nexxyz/octessera/docs/menu-tree-spec.md

# Menu Tree Spec

This file is part of the authoritative menu/control spec rooted at `menu-and-controls-spec.md`. Keep it in sync with native menu tree changes.

This is the canonical index for the full menu tree. The split-out section files below are canonical parts of this spec and exist to keep each prose file navigable.

## Menu Tree (Full)

### Root Menu

```
Root (group)
├── Build (group)
├── Link (group)
├── Shape (group)
├── Play (group)
├── [spacer] (visual separator)
└── System (group)
```

## Split-out sections

- [Build](menu-tree/build.md)
- [Link](menu-tree/link.md)
- [Shape](menu-tree/shape.md)
- [Play](menu-tree/play.md)
- [System](menu-tree/system.md)

The Shape FX bus tree stores Duck `Source Tap` as `pre|post` and displays it as `Pre|Post`; omitted legacy values behave as `Pre`. Exact tap points and excluded stages are defined in [Shape routing semantics](menu-tree/shape.md#routing-semantics).

Short breadcrumb forms use `B`, `L`, `S`, and `P` for Build, Link, Shape, and Play.

The System section puts the dynamic Load Preset shortcut first, followed by Recording, Notes, MIDI,
Audio, UI, conditional SD Card 2, conditional HDMI Video, conditional Bluetooth, Saves, Setup, and Reset. The direct actions
Panic, Sys. Info, Basic Help, Reboot, and Shutdown follow the groups in that order. There is no
duplicate direct Save Current row; `System > Saves > Library > Save Current` is the only Save Current
row. Audio orders conditional USB Audio, conditional HDMI Audio, Master Vol, conditional Perf. Mode,
Polyphony, and Engine; Master Vol keeps key `masterVolume`.
SD Card 2, HDMI Video, and Bluetooth are board-only groups and are omitted on desktop. USB Role is a
Raspberry-capability-only child of Setup before Updates. The complete resolved System order and every
recursive branch are in the [System split-out tree](menu-tree/system.md).

The root Load Preset group contains a `(none)` refresh action and one confirmed action
for each named preset. The same named list remains available under
`System > Saves > Library > Load`.

`System > Notes` owns `Note Length`, `Vel Scale`, and `Vel Curve` with their
existing keys and semantics. `System > Audio` owns `Master Vol`, the supported USB and HDMI audio
mirrors, `Perf. Mode`, `Polyphony`, and `Engine`. `Perf. Mode` is visible on Raspberry and Orange
and displays compact `Lat | Cap` labels for the full `Latency | Capacity` choices; desktop hides it
and all Jack/USB/HDMI/SD2 device controls. `Polyphony` keeps the existing
`sound.voiceStealingMode` values `fixed12`, `fixed16`, `auto-soft`,
`auto-balanced`, `auto-hard`, and `none`. `Engine` contains CPU Warn % and Bus
Idle with their existing keys and values, plus Buf Frames where the
performance-mode capability is unavailable.

`System > MIDI` contains `MIDI Active`, then the conditional `MIDI Host` and `USB Device` groups,
then `Sync / Clock`. `MIDI Host` contains dynamic `MIDI Out` followed by `MIDI In`; it is visible
on desktop and Orange, and on Raspberry only in Host role. `USB Device` contains `USB MIDI`; it is
visible on Orange and on Raspberry only in Gadget role. `MIDI Active` is the global runtime gate and
selects no port or device. USB MIDI enables the bidirectional Gadget MIDI endpoint after restart and
automatically owns both input and output while enabled; Host-selected ports are ignored during that
time. On Orange, those Host selections are retained for later use after USB Device MIDI is disabled.
`System > Setup > USB Role` is Raspberry-only and precedes
Updates. Host hides and disables USB Audio, USB MIDI, and SD Card 2 Start Transfer, while HDMI Audio
and Stop Transfer remain available for cleanup. Gadget does not restore previously disabled outputs.
`System > SD Card 2` contains Start Transfer and Stop Transfer; it exposes the second card to a USB
host only while conflicting USB audio, MIDI, and recording are inactive. HDMI Video contains the
existing Mode, Bars per cycle, and Grid Lines controls. Bluetooth contains the Bluetooth toggle and,
only while it is On, Audio Out, Devices, Pair New, and Forget.
USB and HDMI audio mirror the canonical Jack mix and do not replace it; HDMI audio remains
separate from HDMI video. Restart-sensitive edits use the native Save Setting flow shared with
Audio.

Aggregate audio-load and voice-steal status is separate from the red persistent-
worker CPU icon. The icon is at `(117,5)` and requires valid persistent
`high_cpu_steady` metric; inline or missing metrics hide it. An active
missed-quantum flash takes priority in that CPU slot and inverts the CPU glyph
white/black; the red CPU icon is hidden until the flash clears. The yellow save
icon at `(107,5)` may coexist with either CPU-slot state. A matching newly missed quantum repeats the
previous final master quantum once; subsequent pending-recovery refills are
silent. `missedQuantumFlash` stays true for five emitted seconds, clears on the
exact emitted-frame crossing, and resets on a later miss. The existing OLED
presentation structure and coordinates are unchanged.

The System section's `HDMI Video` group displays `Terminal` for the stored/runtime
value `none`; its `Bars per cycle` row is conditional on `cycle-behaviors`.
See the split-out tree for the framebuffer ownership and snapshot semantics.

Within `System > Saves`, Library precedes Default, then System. Library's Save As,
Load, Rename, and Delete precede Save Current and Refresh List. Within Default,
Auto Save and Backups precede Save Patch and Load Patch; System contains Save System
and Load System. Within
`System > Setup`, conditional USB Role and the Updates submenu precede Configure WiFi, Backup /
Restore, and Hardware Test. Setup rows retain their existing action/config keys. `Configure WiFi`
uses stable key `system.configureWifi`. After confirmation, native runtime stops and resets playback,
sends MIDI panic/note cleanup, never auto-resumes, and emits the typed
setup portal effect. The setup modal reports `starting`, `portal_ready` with
the four-character code and `192.168.42.1` for 10 minutes, `finalizing`,
`succeeded`, `failed`, `timed_out`, or desktop `unsupported`.

`System > Setup > Backup / Restore` is a direct, unconfirmed action with stable
key `system.backupRestore`. On Pi it opens the existing authenticated service
on `http://<regular-ip>:8081` using a generated 10-character code and a
15-minute lifetime. Desktop is unsupported, and the action is separate from
rolling `System > Saves > Default > Backups`, which stores patch-only rolling backups.
