nexxyz/octessera/docs/runtime-boundaries.md

# Runtime Boundaries

This contributor contract keeps UI, host adapters, native runtime logic, core behavior logic, and audio rendering in separate layers.

The shared board-runtime scheduler in `apps/pi-zero/src/hardware_runtime_scheduler.rs` owns Raspberry and Orange timing policy: 8 ms realtime work, 50 ms stopped maintenance, 33 ms playing snapshot cadence/publication gating, native one-shot and continuous display deadlines, bounded wake/input pickup, accepted-revision dedupe/retry, configured sync-source requests, and playing input-snapshot suppression. It contains no board, hardware, audio, adapter, or thread ownership. Both boards run one runtime loop (`apps/pi-zero/src/runtime_loop.rs`) on an `octessera-runtime` thread with one `PiHostAdapter`; between scheduled ticks the loop blocks on the grid/NeoKey/keyboard input channel, so live presses dispatch on arrival instead of at the next tick (encoders and MIDI still use the tick). At startup both board binaries `mlockall` with `MCL_ONFAULT` and lock their own and their libraries' read-only mappings up front, so memory pressure or first use cannot page audio-path code in from the SD card (the services grant `LimitMEMLOCK=infinity`); per-board hooks cover only audio upkeep (Orange recovery, health and readiness; Raspberry load status and Jack fault) and what a power request does.

Authoritative menu/control behavior spec: `docs/menu-and-controls-spec.md`.

## Layer Responsibilities

- UI layer (`apps/desktop/src/`)
  - renders runtime snapshot data
  - captures user interaction and emits `DeviceInput`
  - contains no transport/menu/audio/interpretation logic

- Runtime orchestration layer (`crates/playback-runtime`, `apps/desktop/src-tauri/src/runtime_worker.rs`)
  - owns lifecycle (`start`/`stop`)
  - schedules transport pulses and realtime status through Rust runtime code
  - owns native menu state, config payloads, snapshots, platform effects, and `NativeRunner`
  - owns schema-v2 global modulation state, legacy migration, keyed Link LFO menu/binding paths, canonical global Play XY serialization, and transient global-LFO endpoint composition; it emits resolved audio commands while the realtime engine owns rendering
  - owns the schema-v2 canonical device audio contract: atomic `AudioOutputSet` values for Jack, USB, and HDMI output preferences, the Raspberry-only `UsbDataRole` Gadget/Host contract, Host validation that disables USB Audio and USB MIDI, whole-set validation, strict canonical `audioOutputs` and USB field validation, and next-boot apply confirmation; adapters open the selected exact physical routes under this native contract
  - owns the typed schema-v2 DSP runtime configuration and native `System > Audio > Engine` menu; it emits direct coalescible DSP audio commands without rebuilding prepared audio or changing structural render-plan revisions
  - stamps complete audio configs, instrument owners, FX-slot owners, and safe scalar controls with narrow generations; a complete config establishes generation `G`, immediate child controls use `G`, and the first child replacement advances that owner to `G+1`. Momentary start/update/stop uses a separate instance epoch. These stamps prevent stale controls from crossing asynchronous preparation or owner replacement without introducing a general transaction layer
  - `PlaybackRuntime::dispatch` is the canonical host-message/result observation path; desktop and Pi loops schedule work and render its presented output
  - consumes typed runtime-config changes published by `NativeRunner` during canonical dispatch; hosts must not derive playback scheduling config from snapshots
  - maps typed adapter failure facts to recovery policy and owns the best-effort stop-and-silence operation
  - requires every host adapter to implement internal-audio silence and external-MIDI panic explicitly; safety cannot fall through to a successful no-op
  - classifies worker emission and persistence faults as retain/retry outcomes instead of safety-stop failures
  - applies native core behavior transitions through `platform-core`
  - owns the foldered Note Mapping presentation and selection actions while keeping `pitch.scale` as the persisted wire field; binding and modulation pickers consume the core registry's flat IDs
  - publishes snapshots, including authoritative transient indicator fields and unscaled semantic NeoKey colors, plus platform effects, audio commands, MIDI events, runtime status, and native-owned modal frames
  - PlaybackRuntime owns revisioned OLED production after runtime-error enrichment: typed presentation conversion, two-buffer render/compare cache, monotonic positive frame revision, pending publication, and normalized host metrics. Every emitted snapshot has a positive `oledFrameRevision`; a changed `oled_frame` precedes the referencing snapshot, and unchanged frames publish no pixel payload. Absent or malformed presentation input suppresses the snapshot before the first valid frame, and thereafter applies non-OLED state while retaining the last-good OLED revision and emitting a typed retain-last-good fault/status. Raspberry and Orange normal runtime consumers publish only an accepted frame paired to the snapshot revision: no accepted pair is explicit black, while a missing/future/stale/malformed/conflicting reference publishes immutable accepted bytes as `RetainedLastGood` with a sticky typed fault. The initial acknowledged handoff still requires an exact accepted matching pair. Physical OLED revision advances only after a successful write. Desktop remains a separately gated native consumer; boot, fault, shutdown, suspend, and ownership lifecycle frames remain adapter-owned.
  - Native snapshots require serialized `display.bodyLayout` (`rows` or `card`). `rows` retains existing menu/modal identity, 28-character/7-row normalization, bars, scrollbars, and selected-row scrolling; `card` is used for setup-portal and Backup / Restore status, preserves complete semantic lines, uses the shared 20-column no-scrollbar card rectangle, and reserves the final visual row for its semantic action. `crates/playback-runtime/src/oled_frame/text_layout.rs` owns the fixed-font metrics, normalization, wrapping, and card layout; Pi calls those exported pure functions rather than maintaining a second wrapping algorithm. Concise MIDI rehydration explicitly restores `rows` so a prior status card cannot leak into the MIDI presentation.
  - owns monotonic wall-clock deadlines for the 45 ms event dot and 90 ms beat/measure flash; hosts request timed expiry snapshots and only scale native NeoKey RGB values
  - owns setup-portal menu confirmation, playback stop/reset and note cleanup, the typed `RuntimePlatformEffect::SetupPortalOpen` effect, and all typed setup status/modal presentation
  - owns live Play trigger-gate semantics. Disabling a layer immediately drains held notes owned by that layer from internal Synth, FM, Plucked, and Sampler paths and external MIDI, leaves other layers untouched, suppresses future triggers, and does not resurrect released notes when re-enabled. Already-ringing one-shot Drum hits are not held notes and finish their own decay.
  - owns the portable Data Backup/Restore bundle contract: canonical patch migration and validation, the allowlisted preference delta, manifest/hash metadata, and typed transfer status; it does not perform transfer or filesystem I/O
  - delegates its display-ordered grid index API to the pure fixed-grid projection helpers in `platform-core`; it does not own a second projection table or geometry rule
  - The Orange production service keeps this native ownership through the shared Pi host adapter and Orange-specific construction, audio recovery, and power handling: `octessera.service` runs the native runtime as the locked `octessera-runtime` account, while the separate `octessera` account is for interactive setup and administration. The adapter owns OLED, NeoTrellis, NeoKey, four encoder, store, sample, and MIDI device I/O; Seesaw uses polling and encoder GPIO uses the HAL's gpiocdev v2 edge backend. Internal Synth, FM, Plucked, Drum, and Sampler audio routes through `AudioService` and the realtime engine at 44.1 kHz; MIDI leaves through the native host adapter. Jack is always-on primary on Raspberry Latency and Capacity and Orange Latency and Capacity modes; USB and HDMI audio are independently selectable optional mirrors of the canonical Jack mix, and HDMI audio is separate from HDMI video. Readiness depends on Jack; an absent, waiting, or faulted optional mirror is route-local and never blocks or replaces Jack. The service grants FIFO priority 70 through `LimitRTPRIO=70`; its sole ambient and bounding capability is `CAP_SYS_TTY_CONFIG` for native VT leasing, and it adds no `CAP_SYS_NICE`. Orange USB gadget composition is an image-side adapter decision from `/var/lib/octessera/presets/system.json`: `audioOutputs.usb` controls UAC2 and `usb.midiOutEnabled` controls MIDI, with no gadget, MIDI-only, UAC2-only, and combined states. The staged `usr/share/octessera/defaults/pi-default.json` is immutable image-build metadata, not an active runtime default. The root-owned socket-activated apply lane accepts only the fixed reboot request after validating that persisted System config; it is not a general privilege broker. Orange Check, Apply, and Rollback use the separate root-owned guarded updater lane and only the profile-qualified runtime-updater asset; profile or asset failures stop without a Raspberry, manual-ZIP, or image fallback. The updater does not replace Armbian, kernel, device-tree, or image assets.
  - The production Orange image constructs the AHUB0 vendor dummy-codec route and exact `octessera-dac` playback card (`hw:CARD=octesseradac,DEV=0`) during image construction; it does not use a manual or experimental audio overlay. Selected Orange audio routes also include UAC2 (`hw:CARD=UAC2Gadget,DEV=0`) and HDMI (`hw:CARD=HDMI,DEV=0`) PCMs. Simultaneous physical outputs use independent, unsynchronized clocks and can drift or echo; this phase provides no sample alignment. The Orange HDMI connector path is `/sys/class/drm/card0-HDMI-A-1`; Raspberry runtime code pins the card0 connector identity and does not scan or fall back to card1. HDMI audio is selected independently from video.
  - Orange SD2 transfer source behavior is implemented through the root-owned, exact-command `/run/octessera-orange-storage-control/storage.sock` lane and the shared label-safe SD helper/library. The board/storage adapter owns UDC, gadget mass-storage setup/teardown, local unmount/remount, and recovery handling; the external host owns its eject action.
  - Orange offline DSP profiling is a native `apps/pi-zero` diagnostic branch before hardware startup. It exercises the existing realtime-engine scenarios and reports snapshots; it does not implement playback, control, device, or TypeScript fallback behavior. Orange profiling requires the explicit `--profile-dsp` argument.
  - Orange runtime failure policy is three attempts in a 30-second systemd start-limit window: the initial start plus two `Restart=on-failure` retries at five-second intervals. After that, the unit stays `start-limit-hit` until an operator runs `sudo systemctl reset-failed octessera.service` and then `sudo systemctl start octessera.service`.
  - owns MIDI input/output through host adapters only; Tauri/midir and Pi MIDI device access stay outside canonical runtime crates

- Core logic layer (`crates/platform-core`)
  - deterministic behavior execution, grid state, interpretation, mapping, transforms, and native layer engine logic
  - owns the typed 25-entry note-set registry, category tree metadata, canonical flat IDs, roots, intervals, and root-relative pitch-class expansion; unknown note-set IDs are not expanded
  - generated platform capability constants from `resources/platform-capabilities.json`
  - checked-in generated display palette constants from `resources/display-palette.json`, copied into `OUT_DIR` by the `platform-core` build script, so runtime, Pi, and desktop adapters share color values without moving UI policy into the core
  - owns the fixed 8×8 logical row-major index and logical/display cell and index projection helpers; the lower-left world-space rule is pure native logic, not a runtime projection table
  - no UI framework code
  - no platform-specific I/O
  - no desktop, Pi, Tauri, Node runner, storage, MIDI-device, filesystem, or hardware adapter code

- Output adapters (`apps/desktop/src-tauri/src/`)
  - desktop audio sink maps native events/audio commands to the realtime engine and rodio source
  - desktop and board adapters validate string-path controls into fixed native parameter IDs before audio transport, prepare structural owners and momentary payloads off-callback, and preserve playback-runtime generations/epochs unchanged. Safe latest-value controls bypass preparation queues; complete configs, owner replacements, and previews use bounded preparation lanes
  - desktop `AudioRuntime` retains the rodio `Sink` and constructs the inline `EngineSource` with the existing load-status sender, wrapping that final source once with the desktop recording tap; desktop does not select the Orange routing-tree capacity path or create source-worker lifecycle state
  - MIDI input/output uses Tauri-side midir adapters
  - storage and sample-browser filesystem access remain host adapter responsibilities
  - desktop and Pi retain sample path resolution/containment, caching, preparation, preview/bank orchestration, and typed error adaptation
  - Pi setup adapters own the board-side setup marker and current-status file seam; they do not execute the root coordinator or inspect setup credentials. Data Backup/Restore is not started or advertised by `Configure WiFi`.
  - `System > Setup > Backup / Restore` is a separate native action. PlaybackRuntime owns its action/status/card presentation and existing archive contract; Pi adapters select a usable regular `wlan0` IPv4, bind the authenticated service to `0.0.0.0:8081`, and publish the dynamic URL/code/lifetime. No regular address returns typed unavailable without binding or retry. Desktop returns typed unsupported. The service is never opened through the setup AP or coordinator.
  - Raspberry Pi device-update effects are executed by the host updater, which owns profile-qualified asset selection, checksum/manifest validation, candidate health guarding, and automatic fallback; `NativeRunner` owns menu/action semantics and confirmation. Orange device-update effects are executed by the Orange root-owned broker and guarded updater, which own profile-qualified selection of `octessera-<version>-orange-pi-zero-2w-runtime-updater-aarch64.zip` plus `SHA256SUMS-orange-pi-zero-2w-runtime-updater.txt`, checksum/manifest validation, candidate health guarding, and runtime rollback. Both paths fail closed on board or asset mismatch; neither path selects another board's asset or turns a manual/full-image install into an OTA fallback.
  - returns typed failure facts and carries runtime request/revision identity through asynchronous platform/audio-prep jobs; it does not choose recovery policy
  - Pi `AudioManager` owns the bounded `audio_load_status_channel` sender source; Orange Capacity and Raspberry Capacity primary Jack routing-tree sources receive a sender, and their native runtime loops drain the newest status before snapshot/readiness work. Orange Latency, Raspberry Latency, secondary-route, and benchmark sources publish no load metrics.

- Realtime audio engine (`crates/realtime-engine`, `crates/rodio-engine-source`)
  - owns all internal musical audio rendering, instrument route/pan, FX bus sends, FX bus processing, sidechain ducking, and final stereo mix
  - persistent workers own whole bus chains plus instrument- and bus-targeted momentary FX; CPU1 owns coordinator reduction, global-target momentary FX, global/master processing, and final stereo work
  - optional persistent source-worker rendering keeps one canonical partition+scratch `OwnerEnvelope` per parity plus exactly four logical `BusChainCarrier` positions in lifecycle-owned capacity-one home mailboxes, work/completion transport, worker local state, or a short callback lease; `SourceWorkerRuntime` owns no DSP bundles or bus carriers at callback boundaries, while `SourceWorkerLifecycle` owns fault mailboxes, completion receivers, joins, and final owner destruction. Typed stamped source commands validate runtime, plan, sequence, phase, frame, and sample-clock identity; invalid completions go to fault escrow. Lifecycle-first drop on another thread waits for runtime close; same-thread reverse destruction is prohibited. The default inline path remains available
  - generates synth slot/sample/pan constants from `resources/platform-capabilities.json`
  - `crates/rodio-engine-source` owns shared non-realtime file opening and WAV decoding into `SampleBuffer`, plus refill, previous-master cache repeat/silence, and overload status publication
  - stores the typed DSP worker-warning and bus-idle configuration received through direct control events; evaluates worker warning state only from valid persistent paired completions, while threshold interpretation does not alter prepared audio topology
  - `EngineSource` receives prepared sample buffers and control events; shared file opening/decoding remains strictly outside the audio callback
  - receives an explicit `AllNotesOff` internal command for releasing Synth, FM, Plucked, and Drum voices and clearing Sampler and preview voices; internal safety does not use MIDI CC 120/123
  - separates one atomic emergency fence, an exact ordered musical queue, a bounded structural-owner queue, one latest preview, and fixed latest-value cells for master, DSP, mixer, Synth, FM, Plucked, Drum-kit, Sampler, persistent-FX, and epoch-keyed momentary controls. The callback applies at most 32 latest cells and 256 total control work units, performs at most one retirement-producing owner mutation, and never allocates, blocks, spins, or destroys retired/source-owned heap state
  - accepts control latency and skipped intermediate scalar values to protect musical timing. Notes, Drum hits, and CC remain ordered and are never coalesced. A full or disconnected control lane reports typed overload; terminal retirement pressure fails closed for new NoteOn while preserving NoteOff, CC, and panic service
  - is the only path for Synth, FM, Plucked, Drum, and Sampler internal audio before device output
  - shared JSON audio configuration normalization and FX shape/type validation live in `realtime-engine`; desktop and Pi retain sample preparation, preview/bank orchestration, and typed error adaptation
  - desktop and Pi return the same typed audio-command/config failures, preserve revision identity for full-config preparation, and route `SamplePreview` through the selected realtime instrument path

## Native Audio Recording Boundary

- `crates/media-recording` owns bounded realtime-safe ingress, worker-owned 44.1 kHz stereo signed-16 little-endian PCM WAV writing, MJPG/PCM AVI writing, frame-timeline gap handling, lifecycle, container finalization, and collision-safe partial/final naming.
- `Start Audio` writes WAV under the audio recording root. `St. Audio+OLED` writes an AVI under the screen-recording root with 128x128 MJPG video at 10 fps and 44.1 kHz stereo signed-16 little-endian PCM audio. Audio is the master timeline: each video unit advances every 4,410 audio frames, and the latest accepted OLED frame at or before that tick is held until the next one.
- Desktop resolves its platform Audio/Music directory through Tauri and uses `Octessera/recordings` for audio and `Octessera/screen-recordings` for Audio+OLED. Raspberry defaults are `/home/pi/recordings` and `/home/pi/screen-recordings`; Orange defaults are `/var/lib/octessera/recordings` and `/var/lib/octessera/screen-recordings`.
- Each worker reserves a `.partial.wav` or `.partial.avi` path, syncs and renames it atomically to `.wav` or `.avi` on a complete take, and uses `.incomplete.wav` or `.incomplete.avi` when gaps, ingress overflow, or accepted-OLED material loss occurred. Worker failures retain the partial file; collision-safe reservations add a suffix instead of replacing an existing take.
- PlaybackRuntime owns recording lifecycle presentation: successful starts report `Recording started`, duplicate starts report `Recording is already running`, manual stops report `Recording saved` or `Recording incomplete`, and clean max-duration completion reports `Max time: saved`. While recording is active, the runtime suppresses normal OLED idle sleep without changing the saved sleep setting; when recording ends, normal idle timing restarts. Host adapters own recording ingress and finalization and return these status results.
- Board adapters and the desktop adapter attach exactly one tap to the canonical final stereo mix; mirrored USB/HDMI output callbacks do not create recording owners, and recording ingress performs no filesystem I/O in an audio callback.
- Desktop UI only emits the native recording actions and renders native status; it has no recording or file-writing path.

## Constructor and Respin Boundary

- Board constructors derive images from source-bound boot-layer contracts. Source
  and build metadata establish that derivation.
- `tools/image-respin` has one boot-neutral Orange runtime/setup
  respin lane. It does not replace constructor changes to the image, kernel,
  device tree, or initramfs.
- Raspberry runtime updates do not replace the full image, kernel, or device
  tree. Raspberry full-image update remains manual.

## Vendored CPAL Boundary

- The vendored CPAL path and exact patch are documented in
  [`third_party/cpal-0.15.3/PROVENANCE.md`](../third_party/cpal-0.15.3/PROVENANCE.md).
  The patch affects direct Pi CPAL use and desktop/rodio transitively.
- Its boundary is exact fixed-board ALSA PCM opening and host mechanics only:
  typed host errors, stream/buffer/pause/play/wakeup/teardown semantics, and
  WASAPI compatibility.
- Runtime and adapters retain route-selection policy. Broad device discovery and
  fallback are not authorized; CPAL does not own DSP or mixing.
- Rebase or removal requires exact PCM and provenance/legal review.

## Setup Portal Boundary

- `crates/playback-runtime` owns the menu/effect/status presentation. It does not execute setup, authorize a request, or resume playback after setup.
- For this seam, the fixed Pi adapters create exactly the `start\n` marker at `/run/octessera-setup-request/inbox/start`, then read only `/run/octessera-setup-status/current.json`. They do not read root-private control state, credentials, or setup secrets.
- The enabled path unit starts the only root-owned `octessera-setup.service`. The pinned patched `wifi-connect` owns the AP, DHCP, HTTP portal, and network switch; the coordinator owns country handling, setup-value validation and in-memory holding, finalization, cleanup, and the one current status file. The confirmed instrument `System > Setup > Configure WiFi > Open Portal` action triggers this path; a fresh production image does not start an automatic hotspot. The AP user window is 10 minutes after readiness. Browser submission is provisional, and an AP disconnect is not a result; the OLED terminal result is authoritative. Success requires a usable global `wlan0` IPv4 address only, not Internet access, a default route, DNS, or ICMP, then directs the user to `System > Sys. Info` without a reboot.
- Desktop returns typed `unsupported` setup status. No TypeScript behavior, `sudo`, `systemctl`, secret handling, root-private state access, network discovery, or fallback path belongs in the runtime or desktop UI.
- `System > Setup > Backup / Restore` is a separate direct action and does not use this setup boundary. Its Pi service selects a current usable regular `wlan0` IPv4 address, binds `0.0.0.0:8081`, uses a generated 10-character code for 15 minutes, and reuses the active session on reopen without extending it. Back only hides the OLED card; Stop closes the service and revokes the code. Expiry or authentication revocation closes it, while the existing physical restore confirmation and restore-time input barrier remain native contracts.
- Data Backup/Restore archive validation and preference projection stay in `crates/playback-runtime`; Pi host code owns archive/media I/O and applies a physically confirmed, staged restore. Confirmation is consumed atomically before adapter status draining, publishes the typed native `RuntimeUserDataRestoreStatus { phase: RuntimeUserDataRestorePhase::Restoring }` snapshot with `Restoring...`/`Please wait`, consumes normal device input until the worker reports `Succeeded` or `Failed`, and serializes the restore with platform store jobs and direct System/patch saves. Ambiguous swaps retain their `.old`/`.new` recovery trees and the pre-restore archive. The `.oct` archive carries music and selected portable preferences, with optional media; destination-local USB role, MIDI/audio endpoint IDs, and favourites remain local. Credentials, binaries/images, and hardware identity remain outside the portable bundle.

## Device Apply Boundary

- Orange's `/run/octessera-device-apply/reboot.sock` is a root-owned, group-limited systemd socket for exactly two requests: `reboot\n` and `poweroff\n`; it remains one fixed socket for compatibility and does not discover or select commands.
- `octessera.service` requires and starts `octessera-device-apply-reboot.socket` before the runtime; the socket is enabled separately through `sockets.target` and waits only for `local-fs.target`. Musical-default provisioning remains an independent runtime prerequisite, not a socket prerequisite. This dependency only repairs socket activation ordering and does not change the helper protocol or security boundary.
- The socket service validates the regular `/var/lib/octessera/presets/system.json` file, its expected runtime ownership/mode, and the canonical audio/gadget schema only for `reboot\n`, then invokes only `/usr/bin/systemctl reboot` or `/usr/bin/systemctl poweroff` for the matching exact request before returning `accepted\n`; malformed, unknown, extra-byte, timeout, or failed requests return `rejected\n` without invoking another command.
- Native Rust owns the confirmed save/apply/shutdown semantic and sends these fixed requests through the adapter lane after external MIDI panic and internal audio silence. The image helper owns only the fixed request validation, reboot config validation, and power command execution; it does not accept command arguments, config payloads, or arbitrary commands. Orange has no `octessera-runtime` sudoers entry.
- When Internet is available, `System > Setup > Updates` uses the separate root-owned `/run/octessera-update/update.sock` broker for Octessera runtime-only `check\n`, `apply\n`, and `rollback\n` actions. The broker invokes the guarded updater and returns bounded results; it does not expose a general command or privilege broker. The updater changes only the managed runtime release and binary link. Full Armbian, kernel, device-tree, and image replacement remains a manual image operation, and the standalone manual runtime ZIP is not an OTA asset.
- Orange SD2 transfer uses a separate root-owned `/run/octessera-orange-storage-control/storage.sock` socket. Its systemd service accepts only one bounded `storage-start\n` or `storage-stop\n` request from `octessera-runtime`, invokes only the fixed storage action, and returns bounded `accepted`/`rejected`, sanitized `HOST_STATE`, and error fields. The lifecycle owns the shared SD-card/gadget locks and state, refuses root/parent/wrong/duplicate-label candidates, never binds while locally mounted, and restores the configured UAC2/MIDI gadget after a successful stop. This is a source/image contract, not physical Orange USB or host-eject testing; Orange has no storage sudoers entry.
- Raspberry USB data-role apply is a board adapter transaction: the native runtime saves the confirmed setting to the System file, and the Pi worker serializes the validated role comparison, atomic System write, exact `sudo -n /usr/local/sbin/octessera-usb-role host|gadget` call, and byte-for-byte rollback on ordinary helper failure. Host apply is rejected before writing when the authoritative SD2 state exists; the root helper changes only the exact managed `dtoverlay=dwc2,dr_mode=...` line in the single `[all]` block. Systemd skips gadget setup in Host mode; SD2 start rejects Host before mutation, while SD2 stop remains available to validate active state, tear down mass storage, remount the original SD when required, remove state, and leave the gadget absent. A successful apply only schedules the existing reboot lifecycle. Constructor/provisioning own helper installation and boot reconciliation; deploy-fast and runtime updates do not mutate boot configuration.

## OLED Boot Handoff Boundary

- The final systemd paths on the fixed Raspberry Pi Zero 2 W and Orange Pi 2W use the same source-defined OLED boot sweep from `resources/oled/boot-sweep-v1.json`: the mounted SSD1351 controller origin decreases by 303 px while the physical panel motion is left-to-right. In canonical bottom-to-top coordinates the top-row origin is 127 px less X than the bottom-row origin (`bottom_origin - row_y`); this produces the physical-panel slash, with green, magenta, cyan, and yellow bands reading left to right (the Build, Link, Shape, and Play menu colors), 8 px bands, and 4 px separators. The sweep uses 30 frames over a 1,200,000,000 ns cycle (25 fps); the clean logo+wordmark frame follows it and continuous boot loops retain that frame for a responsive 2,000,000,000 ns inter-loop rest. This is a source and test contract; exercise hardware output through the board test procedures.
- Normal first boot is not designed to wait six minutes. Upstream filesystem resize is ordered before runtime, and six minutes is only the upstream maximum timeout; the normal animated splash covers this boot work. Raspberry and Orange root-installed systemd animators are the sole loops and run concurrently with service loading after their fixed OLED devices are ready. Raspberry explicitly wants and waits for `systemd-udev-settle.service` before opening its GPIO/SPI devices; it does not depend on unavailable device units or polling. Either board may remain blank until systemd starts its animator. Native startup requests release, waits for the shared OLED lock, adopts the already-initialized display without reset, and stops the animation or persistent handoff status immediately before publishing the acknowledged first normal menu frame. If native ownership has not arrived by the 30-second handoff window, both board source paths write one static polished `STARTUP DELAYED` / `PLEASE WAIT` frame and continue polling the same handoff state as the sole OLED writer. The frame is delayed-start legibility/recovery mitigation. A matching stop request releases without black/off; only genuine writer errors or termination signals use the black-frame/display-off failure cleanup. Sleep and shutdown are separate OLED lifecycle paths, not boot-handoff states.
- Native runtime owns the confirmed instrument-menu lifecycle presentation. `Going to sleep`, `Shutting down`, and `Rebooting` are exact native toasts over the shared static `SPLASH_SLEEP_SHUTDOWN` background and existing toaster geometry. Ordinary Reboot and Shutdown use one board-neutral lifecycle: the recovery save must succeed, the lifecycle atomically accepts the terminal transition and stops non-terminal follow-ups/input, it independently attempts external MIDI panic and internal audio silence, then only after both succeed force-publishes and physically acknowledges the latest terminal snapshot, zeros the grid and NeoKey LEDs, preserves the OLED pixels/on state while detaching its handles, and finally invokes the board adapter's fixed power path. Save, safety, or terminal acknowledgement failures never submit power; power submission failures leave the accepted lifecycle closed and are reported as typed/logged failures. This contract does not claim presentation for arbitrary administrative `systemctl poweroff` or `systemctl reboot` commands.
- Orange's boot-loop handoff has a monotonic 30-second deadline that begins immediately after `handoff.start()`, before OLED initialization or adoption. At the deadline it writes the static `STARTUP DELAYED` / `PLEASE WAIT` frame once and keeps polling; matching stop requests release without black/off. Genuine errors or termination signals attempt an exact 32768-byte black RGB565 frame, then display-off `0xAE` independently, close once, and publish one attachable `failed` state. A failed handoff keeps the current boot ID and matching valid request ID so native recovery can attach it. Signal handlers only set a flag and do no I/O.
- Orange startup-fatal presentation is adapter-owned and fixed: `GRID NOT FOUND`, `NEOKEY NOT FOUND`, `CONTROLS NOT FOUND`, `AUDIO NOT FOUND`, `OLED NOT READY`, or generic `STARTUP FAILED`. The splash remains the sole OLED writer; it gives short power/connection guidance. A fatal frame is bright initially, redraws once at a dim but readable level after 60 seconds if unchanged, and becomes bright again with a changed code; detailed causes remain in the `octessera.service` journal (`journalctl -u octessera.service --no-pager`). Power must be off before checking or reseating connections. Raspberry's corresponding change here is logo-only delayed-frame cleanup and does not consume the Orange fatal state.
- Orange runtime failure does not stop or mask NetworkManager, and it does not stop an already-enabled SSH service. Fresh images keep SSH off until setup selects a key or password, and setup enables SSH only for those two modes. Wi-Fi association after a warm reboot is not guaranteed.
- An unconfigured Raspberry image keeps SSH disabled without masking its vendor SSH units, so explicit Raspberry Pi Imager customization can enable it. Imager customization must retain the fixed `pi` username because the Raspberry runtime requires that account; the setup portal's SSH-off choice remains unchanged.
- Orange NeoTrellis operation requires the exact validated bus, wiring, and addresses; adapters do not provide an alternate bus, address, or hardware fallback.
- The menu `OLED Sleep` setting is display-only UI behavior. Linux suspend is a separate Orange `sleep.target` ownership transaction. Production installs `octessera-orange-oled-suspend.service` through `RequiredBy=sleep.target`, creating the hard `sleep.target.requires` relationship rather than a `.wants` relationship; a failed preparation therefore blocks suspend. The runtime quiesces and preserving-detaches its OLED handles, a strict AF_UNIX helper renders the suspend/resume frames, and the runtime reacquires the lock and hardware without changing the established `first_menu_rendered` handoff phase. Audio, MIDI, transport, and LED contracts remain unchanged.
- The board runtime owns `/run/octessera-boot`, including `oled.lock`, `status.json`, and `stop.request`. The lock is exclusive: the animator, native runtime, and lifecycle utilities may not write the OLED concurrently. `status.json` uses the strict phases `animating`, `release_requested`, `released`, `native_owned`, `first_menu_rendered`, and `failed`; the normal path reaches `first_menu_rendered`, while matching failure state remains attachable for recovery.
- First-menu readiness requires an actual OLED write acknowledgement. Every valid Pi audio set includes always-on Jack, and readiness depends on Jack. Optional USB or HDMI mirrors may be absent, waiting, or faulted without blocking or replacing Jack. A snapshot being queued, or a runtime service merely starting, is not readiness.
- Normal Raspberry and Orange output apply their board-specific clockwise RGB565 framebuffer transform (`source (x, y) -> transmitted (127 - y, x)`) in the HAL before writing accepted native RGB565BE bytes. Orange uses a reusable 32 KiB transform buffer, preserves RGB565 byte pairs, and keeps SSD1351 remap `0x74`. The Python splash is a separate renderer with the same physical orientation; its SSD1351 command byte is sent with D/C low and command data with D/C high, matching the Rust transport framing.
- HDMI `Terminal` leaves Linux in control of `/dev/tty1`; native grid output takes a native VT lease around `/dev/fb0` and restores text on release. It does not force a connector or start/use a display server. A missing framebuffer or transient open, geometry, or write failure is nonfatal and retried. During boot handoff the splash is an observer until `first_menu_rendered`; a native startup fatal condition lets it reclaim OLED presentation for the typed fatal frame. These are source contracts; hardware display behavior is exercised separately.
- Raspberry's selected initramfs writes one clean logo+wordmark frame and does not sweep, loop, publish a marker, or adopt the OLED. Its root-installed systemd service remains the sole animator and runs concurrently with service loading; Orange's selected initramfs likewise writes one static RGB565 frame with its fixed Python closure, while its root-installed renderer, lifecycle modules, assets, and `octessera-orange-boot-splash.service` remain the only loop. These are adapter differences around one shared handoff contract.
- Boot source, service, and selected-initramfs changes are constructor-required for both boards. The Orange runtime respin lane is boot-neutral and does not apply to this layer.

## Dependency Rules

- UI may import type contracts and render snapshots only.
- UI must not call native core, transport, audio, MIDI, or storage bridges directly.
- Runtime may import native core and output/input adapters.
- Core crates must stay platform-agnostic.
- `crates/platform-core` and `crates/playback-runtime` must not depend on Tauri, HAL, Pi hardware crates, Node runner processes, storage implementations, or host filesystem/sample-browser adapters.
- Platform adapters must not create independent musical audio sinks that bypass the realtime engine mixer.

## Data Flow

1. UI interaction -> `DeviceInput`
2. Runtime receives input -> native `platform-core` transition through `NativeRunner`
3. `NativeRunner` publishes typed runtime-config changes -> `PlaybackRuntime` updates transport/MIDI scheduling state
4. Rust runtime advances transport pulses -> native behavior/menu processing
5. Runtime publishes snapshot -> UI render (OLED + NeoKey LEDs)
6. Runtime publishes musical events/audio commands/platform effects -> host adapters (audio/MIDI/storage)

## Shared Runtime Contract

- The shared Pi/desktop playback seam is defined by `crates/playback-runtime/src/protocol.rs` and mirrored by the UI/device contract types where needed.
- Host -> runner messages are limited to `device_input`, `transport_pulse_step`, split MIDI realtime wire messages (`midi_realtime_clock`, `midi_realtime_start`, `midi_realtime_continue`, `midi_realtime_stop`), and `runtime_result`.
- Runner -> host messages include `snapshot`, optional `oled_frame`, `platform_effects`, `musical_events`, `midi_events`, `audio_commands`, and `runtime_status`. Every `snapshot` leaving `PlaybackRuntime` carries a positive OLED revision. `oled_frame` is changed-frame-only and precedes its matching snapshot; Raspberry and Orange pair accepted native frame bytes to normal snapshot publication or retained-last-good bytes during a typed cache fault; desktop remains a separate native consumer.
- Shared fixtures for this seam live in `SHARED_RUNTIME_CONTRACT_FIXTURES` so both hosts can validate the same contract examples.
- `transport_pulse_step` is the deterministic PPQN advancement boundary; hosts must not substitute wall-clock timer semantics above this seam.
- External MIDI realtime (`clock`, `start`, `continue`, `stop`) remains explicit at the boundary and is not inferred from UI/runtime scheduling code. Desktop MIDI input is routed natively from the host adapter into the runtime worker; UI code must not observe raw MIDI bytes for display or transport state.
- `runtime_result` carries host-side outcomes for storage, MIDI port enumeration/selection, sample-browser operations, device-update status, and asynchronously identified sanitized system-info requests back into the shared runner.
- `SystemInfoRequest` is a typed platform request; adapters return typed `SystemInfoResult` or identified `SystemInfoError` values. The native runner owns loading/error/unavailable presentation, row formatting, clipping, scrolling, and dismissal. Desktop UI renders only the resulting snapshot/OLED frame.
- `NativeRunner` may emit an internal typed runtime-config change during dispatch; `PlaybackRuntime` consumes it before returning presented host messages. It is not a host adapter responsibility and is never reconstructed from snapshot fields.
- Central modulation processing is the single native path for held tick/XY sources and global LFO output: behavior ticks and active XY captures update held sources, global LFOs advance only at 24 PPQN, and the process sums persistent, held, and LFO contributions, clamps once, and applies once per target endpoint. An active LFO step processes only dirty LFO endpoints plus other contributors sharing those keys; unrelated held grid/XY sources are retained without being resolved, reapplied, or cloned. Ordinary menu/Aux base edits rebase and recompose only the edited key/endpoint, preserving held sources so clearing a source restores the new base; changed persistent targets from one tick share one revision and delayed autosave request. Config/patch transactions reset candidate modulation state, install every persistent owner, then resample active XY so its captured base is the loaded owner value. Enabled targeted LFO phases advance and wrap even at depth zero; XY smoothing is the separate native monotonic-elapsed-time path for mapped normalized axes and does not move into desktop TypeScript or realtime-engine code.
- Background audio preparation returns identified typed success/failure results through `runtime_result`; prep failures retain the last good runtime/audio state.
- Sample-bank preparation is atomic on both hosts: every configured sample path must resolve and decode before a new bank is queued; unresolved or undecodable samples return typed `sample` failures and leave the previous banks and signatures in place. Sample preview resolution/decoding runs on the audio-prep worker, never on the runtime or host-adapter thread, and reports success only after the prepared preview reaches the audio queue.
- Pi audio preparation treats superseded revisions as cancellation: no stale-prep fault is returned or latched.
- Identified asynchronous results retain their request ID/revision through the runner round trip; `PlaybackRuntime` observes each result once and clears only the matching fault.
- Emission and persistence faults clear only after the corresponding native emission or identified save/recovery acknowledgement succeeds. Native save confirmation/toast feedback is emitted after that acknowledgement, not when a save request is queued.
- `octessera.patch` schema version 2 carries musical patch state, while `system.json` carries local System settings. Native edit classification saves ordinary System preferences only after a changed editor exits with Main or Back; unchanged or reverted edits do not save, parameter turns do not write individually, and these preferences do not dirty the musical patch. When a System write is pending, only the latest completed snapshot is retained for a follow-up write rather than guaranteeing a physical write for each overlapping edit. Pi and desktop adapters perform the atomic write on their existing platform workers, off the runtime thread, and return an identified completion that updates the save baseline. Explicit System Save remains available; restart-sensitive settings persist only after confirmed Apply. Confirmed System Load changes settings without stopping music or silently rebooting. Reboot and Shutdown refuse with `System save pending, try again` while a System write or follow-up remains pending; an allowed shutdown preserves Patch-only recovery. Local `default.patch.json`, autosave backups, and recovery may retain safe relative user/SD sample references; named presets and `.oct` musical exports remain portable only with canonical shipped-library IDs. Device/System aux bindings stay local; musical aux bindings travel with the patch. Patch autosave, rolling backups, and recovery are patch-only. Confirmed Patch/Named Load stops and resets music, sends MIDI panic/note cleanup, and retains local System settings and ports. A pending patch write or Auto Save-eligible dirty patch blocks load with `Save pending, try again`; with Auto Save off and no pending write, the normal confirmation can discard dirty patch edits. Portable parity for named presets and `.oct` musical state requires valid shipped-library sample IDs, not equality of the full device config. Data Backup/Restore `.oct` archives carry music and selected portable preferences, optionally media, but are not full System backups or device clones.
- Stop-and-silence recovery independently attempts runner transport stop, internal instrument silence, and external MIDI panic on both hosts.
- `snapshot` is the runtime display/input-facing state payload; `musical_events`, `drum_hits`, `midi_events`, `platform_effects`, and `audio_commands` are the resolved outputs that Rust schedules or dispatches.
- `oled_frame` carries a positive revisioned 128×128 `rgb565be` Base64 payload on the JSON bridge; typed native pixels remain immutable bytes before serialization. Desktop, Raspberry, and Orange adapter caches stage candidates and promote only on matching snapshot references, validate dimensions, format, Base64, exact byte length, revision idempotency/conflicts, and expose sticky typed cache faults. Same-revision byte conflicts remove candidates or poison accepted revisions until a strictly newer valid snapshot matches. Raspberry and Orange normal OLED publication consumes accepted native bytes with no semantic renderer fallback; before acceptance they publish explicit black, and after acceptance they retain last-good bytes rather than black on a bad reference.

## Audio Routing Contract

- The shared runtime audio rate is 44.1 kHz.
- Internal Synth, FM, Plucked, Drum, and Sampler instruments must enter the realtime engine before audio output.
- Instrument `Route=direct` bypasses FX bus processing and pans directly into the main mix.
- Instrument `Route=fx_bus_n` enters the selected FX bus, runs its slot FX in order, then pans into the main mix.
- MIDI instruments emit external MIDI/control data and are not an internal audio source unless an audio return path is explicitly added.
- MIDI-only instrument notes and CCs use the `midi_events` path and must not call host internal-audio musical event handling.
- Sample browser preview is musical audio and must route through the selected instrument slot, pan, volume, FX bus, and master output path.
- The default sample artifact has 320 media files: 318 WAV files are loadable through the sampler browser/decoder, and two AIFF files remain outside that WAV-only load path. The technical integrity manifest is not a runtime attribution mechanism.
- Raspberry, Orange, and desktop audio recording tap the canonical final stereo mix once; recording ingress carries absolute session audio-frame offsets and never performs filesystem I/O in an audio callback.
- Runtime audio config commands carry `sound.voiceStealingMode`; host adapters forward it to the realtime audio policy.
- Raspberry and Orange startup read `runtimeConfig.sound.optimizeFor` as the authoritative local DSP mode. Raspberry Latency constructs the inline Jack path with output 256, ALSA period 64, internal block 128, and zero lookahead; Raspberry Capacity constructs the routing-tree Jack path with output 256, ALSA period 64, internal block 256, and 256-frame lookahead. Orange Latency constructs the inline Jack path with output 128, ALSA period 32, internal block 32, and zero lookahead; Orange Capacity requires Jack and constructs the routing-tree Jack path with output 256, ALSA period 64, internal block 128, and 128-frame lookahead. Neither board uses persisted `audioOutputBufferFrames` to choose its construction geometry; Desktop remains inline.
- `gridBrightness` is applied by core LED frame rendering; `displayBrightness` is owned by `PlaybackRuntime`'s OLED presentation conversion and carried into native frame bytes; `buttonBrightness` is applied by desktop and Pi only to the native unscaled `neoKeyLeds` values with the shared basis-point dim rule.

## Grid Coordinate Contract

- Core logic uses a world-space grid origin at lower-left: `(0,0)` is bottom-left, `y` increases upward.
- UI/hardware-facing layers may use screen-space coordinates (top-left origin), but conversion is only allowed at boundaries.
- `platform-core` owns the fixed 8×8 pure logical row-major and logical/display projection helpers. `playback-runtime` delegates its existing display-index API to those helpers.
- `packages/device-contracts/src/gridDomain.ts` is the deliberate TypeScript boundary mirror for desktop input/rendering; it is checked against the exhaustive `resources/grid-projection-v1.json` fixture.
- The HAL keeps fixed NeoTrellis quadrant/key wiring separate from the native projection owner. Its four-device addresses, physical key ordering, and GRB output are adapter facts, not generic geometry.
- In code, grid coordinate conversion must go through these centralized boundary helpers rather than ad-hoc math; the checked fixture is verification data, not a runtime table.
