nexxyz/octessera/userdocs/data-backup-restore.md

# Data backup and restore

Use `System > Setup > Backup / Restore` on a Pi before reflashing. The `.oct`
archive carries music, selected portable preferences such as brightness, and
optionally user media.
It is not a complete System backup or a device clone: USB role, MIDI/audio
endpoint IDs, and favourite folders stay with the destination instrument.
Ordinary System preferences save separately from the musical patch. Rolling
saves and recovery backups protect the musical patch only.

## Save local settings and music

Changed ordinary local preferences, such as display brightness and Auto Save,
save once when you leave their editor with Main or Back, not on every turn;
unchanged or reverted edits do not save. You can still use
`System > Saves > System > Save System` to save settings explicitly, or
`System > Saves > System > Load System` to load them. Load System asks for
confirmation but does not stop music or silently reboot. Restart-sensitive
USB and audio-output choices save only after confirmed **Apply**. If a System
save is still underway, Reboot and Shutdown refuse with `System save pending,
try again`; press again once it finishes.

Use `System > Saves > Default > Save Patch` to save and
`System > Saves > Default > Load Patch` to load the local musical default, not
device settings. An eligible Load Patch asks for confirmation; a confirmed load
stops and resets playback and clears held notes. If a patch save is pending or
an Auto Save-eligible edit is still dirty, it refuses with `Save pending, try
again`. With Auto Save off and no pending write, confirmation may discard
unsaved music. Named presets under `System > Saves > Library` are musical and portable.
Patch autosaves, rolling backups, and recovery copies protect patches only;
they do not back up System settings. Changing the Auto Save preference is a
System setting: it saves after a changed editor exit and does not immediately
save the musical Patch.

## Back up your data

1. On the Pi, choose `System > Setup > Backup / Restore`.
2. The OLED Ready card shows the regular network `IP`, `PORT 8081`, a generated
   10-character `CODE`, and the remaining lifetime. Build `URL` as
   `http://<regular-ip>:8081` and use the displayed code.
3. Download the backup:

   ```sh
   URL="http://<regular-ip>:8081"
   CODE="<10-character code shown on the OLED>"
   curl -fL -H "X-Octessera-Transfer-Code: $CODE" \
     -o octessera-user-data.oct "$URL/export"
   ```

   To include optional user media, use `$URL/export?media=1` instead. Keep the
   downloaded `octessera-user-data.oct` somewhere safe before removing or
   flashing the source card.

   A patch that assigns a local or SD-card sample cannot go into a portable
   `.oct` archive, even with `media=1`. Export refuses that patch instead of
   silently dropping its assignment. Keep a separate copy of those WAVs; use
   shipped-library samples when you want the patch itself to travel.

If no regular network address is available, the action cannot start. **Back**
hides the Ready card while the transfer remains available. Choose **> Stop service**
when you are finished; the code also expires automatically.

## Restore your data

Restoring replaces the destination's current user data. Export it first if
there is anything on the fresh board you want to keep.

1. Export from the old board before flashing it. Include media for supported
   extra files and saved recordings; see the local-sample warning above.
2. Save `octessera-user-data.oct` somewhere off the board.
3. Flash the matching Raspberry or Orange image and complete its normal first
   boot and network setup.
4. On the fresh board, choose `System > Setup > Backup / Restore` again. Use the
   new `URL` and OLED code:

   ```sh
   curl -f -X POST --data-binary @octessera-user-data.oct \
     -H "X-Octessera-Transfer-Code: $CODE" "$URL/restore"
   ```

5. The upload prepares the restore but does not change your data yet. When the
   OLED asks for confirmation, press the Main encoder to apply it or **Back** to
   cancel. During the restore, the OLED shows `Restoring...` and `Please wait`,
   and normal input is blocked.
6. Wait for the final result before stopping the service or powering down. An
   invalid upload or a failure before applying it leaves the destination data
   in place. If reloading fails after the store tree is replaced, the
   instrument reports failure and blocks saves; it does not automatically
   roll back to the old tree. Keep your source card and downloaded archive.

Never remove power, the storage card, or the board's microSD card during a
transfer or restore. Do not erase the source card until the backup file is
downloaded and safely stored.

`System > Saves > Default > Backups` controls rolling local patch backups, not
System settings. Keep a separate copy of any device settings you need to record;
the `.oct` archive is portable by design, not a full instrument clone. The OLED
SD2 `octessera/saves` directory is also separate; copy it manually when you
want to preserve those files.
