nexxyz/octessera/samples/SOURCE.md

# Bundled samples

Octessera's bundled samples come from the attribution-free [stargate-sample-pack](https://github.com/stargatedaw/stargate-sample-pack).
