nexxyz/octessera/assets/octessera-pi-sleeping.png

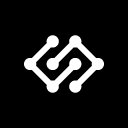
assets/octessera-pi-sleeping.png
