nexxyz/octessera/hardware/enclosure/step/case_bottom_plate_cadquery.step

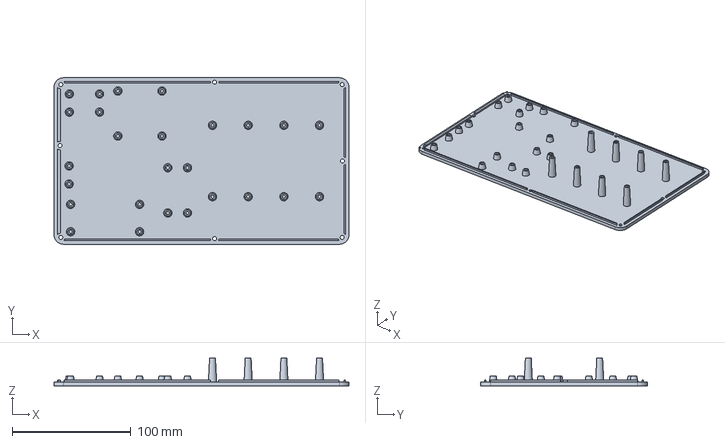
[picture p16: CAD file, 2026-09-16]
hardware/enclosure/step/case_bottom_plate_cadquery.step
248.0 x 140.0 x 23.2 mm
