nexxyz/octessera/hardware/enclosure/3mf-multicolor/mx_keycap_play_multicolor_flush.3mf

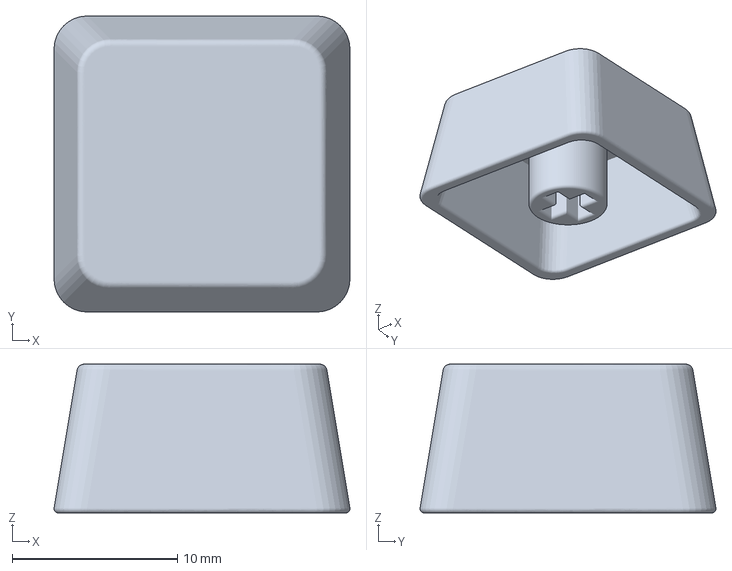
[picture p17: CAD file, 2026-09-16]
hardware/enclosure/3mf-multicolor/mx_keycap_play_multicolor_flush.3mf
17.9 x 17.9 x 9.00 mm
