nexxyz/octessera/hardware/enclosure/3mf-single-material/standoff_pillar_10mm.3mf

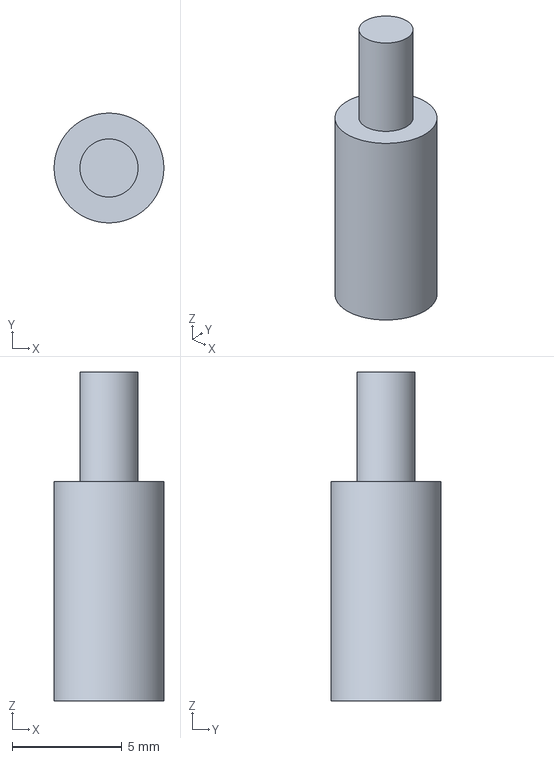
[picture p18: CAD file, 2026-09-15]
hardware/enclosure/3mf-single-material/standoff_pillar_10mm.3mf
5.00 x 5.00 x 15.0 mm
