nexxyz/octessera/hardware/enclosure/step/standoff_top_pin_thin_base.step

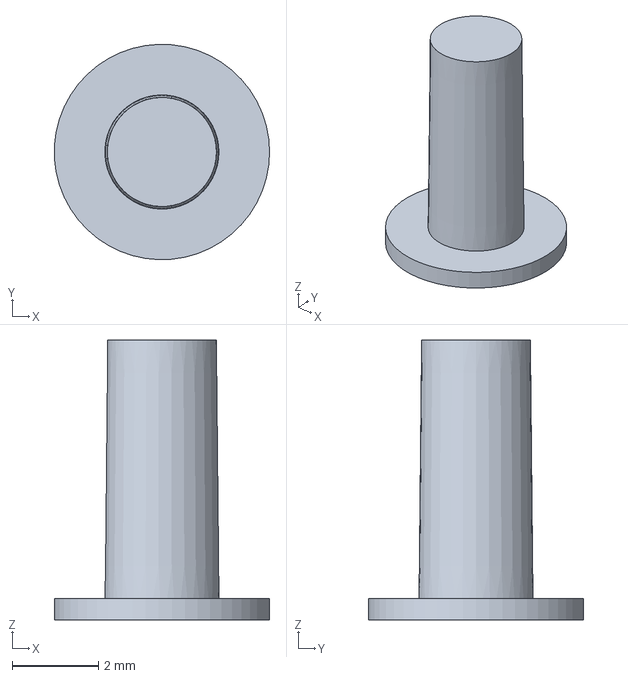
[picture p19: CAD file, 2026-09-16]
hardware/enclosure/step/standoff_top_pin_thin_base.step
5.00 x 5.00 x 6.50 mm
