nexxyz/octessera/hardware/enclosure/3mf-multicolor/protective_case_deep_tub_multicolor_logo.3mf

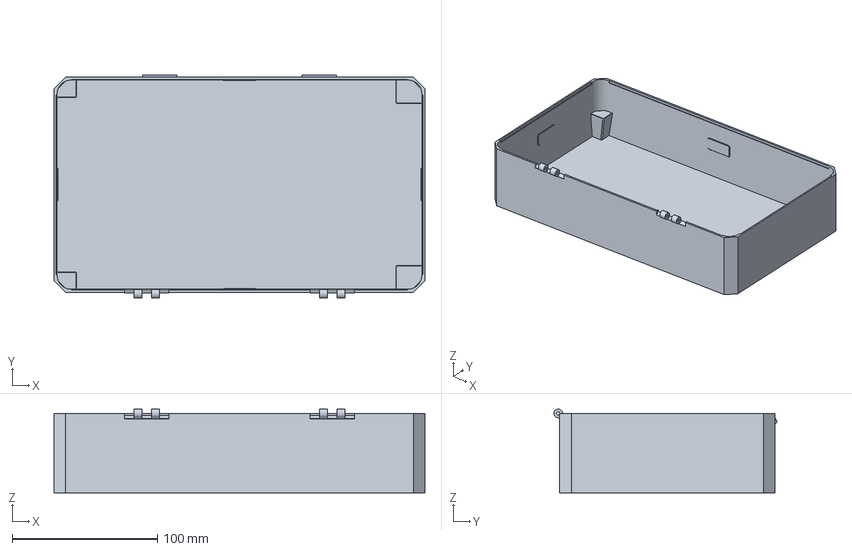
[picture p20: CAD file, 2026-09-16]
hardware/enclosure/3mf-multicolor/protective_case_deep_tub_multicolor_logo.3mf
255.6 x 153.8 x 57.8 mm
