nexxyz/octessera/hardware/enclosure/3mf-multicolor/protective_case_shallow_lid_multicolor_branding.3mf

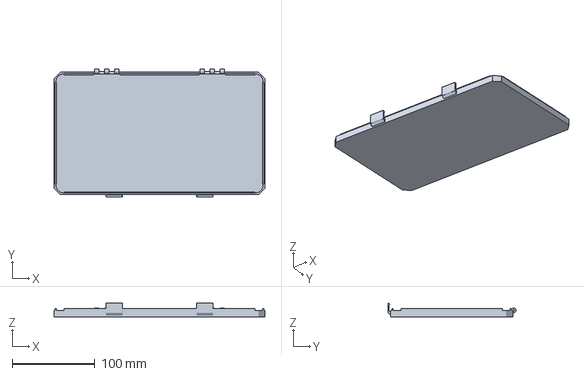
[picture p21: CAD file, 2026-09-16]
hardware/enclosure/3mf-multicolor/protective_case_shallow_lid_multicolor_branding.3mf
255.6 x 155.4 x 16.8 mm
