nexxyz/octessera/hardware/enclosure/3mf-single-material/encoder_cap_aux2_ribbed_dots.3mf

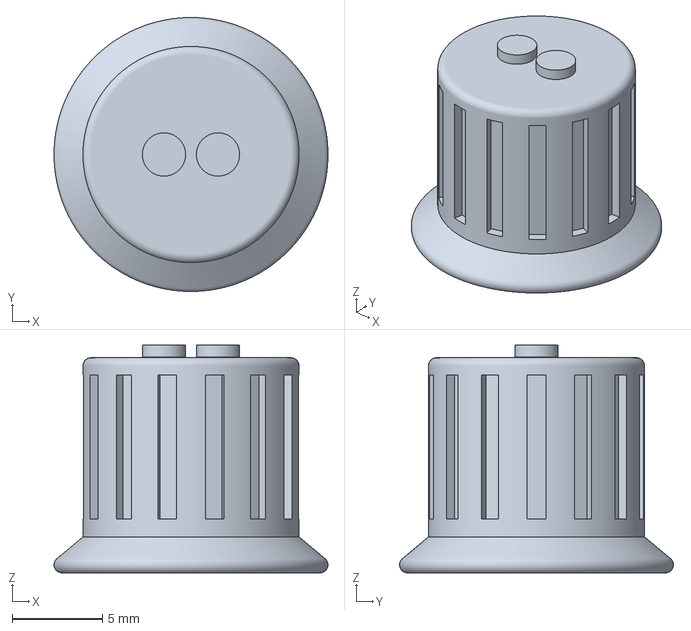
[picture p22: CAD file, 2026-09-15]
hardware/enclosure/3mf-single-material/encoder_cap_aux2_ribbed_dots.3mf
15.2 x 15.2 x 12.7 mm
