nexxyz/octessera/hardware/enclosure/3mf-single-material/friction_insert_spreading_pin_headed.3mf

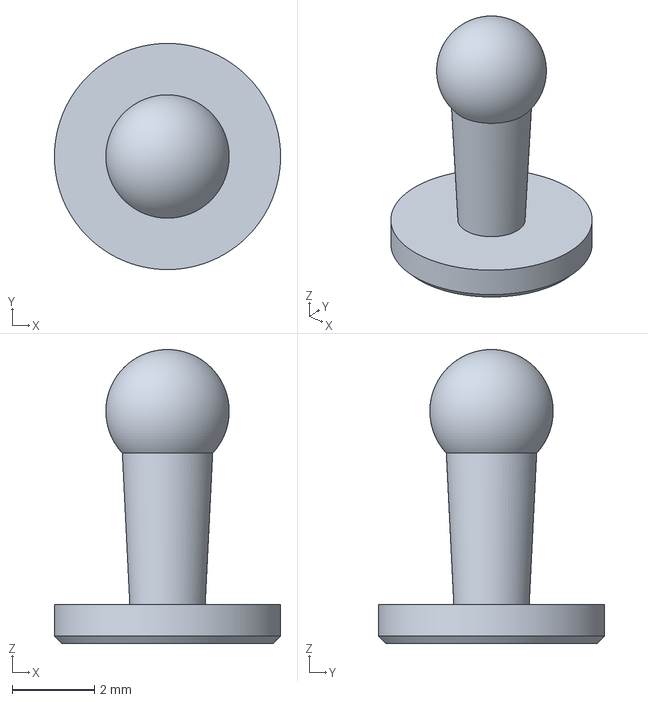
[picture p23: CAD file, 2026-09-15]
hardware/enclosure/3mf-single-material/friction_insert_spreading_pin_headed.3mf
5.50 x 5.50 x 7.15 mm
