nexxyz/octessera/hardware/enclosure/step/friction_insert_expanding_plug_flat_sides.step

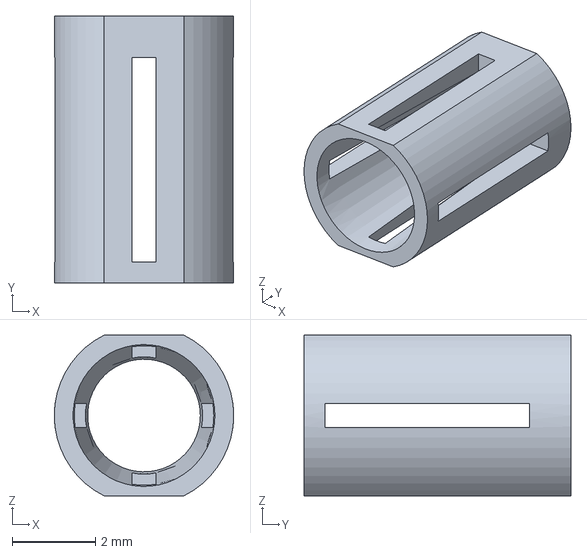
[picture p24: CAD file, 2026-09-16]
hardware/enclosure/step/friction_insert_expanding_plug_flat_sides.step
4.30 x 6.40 x 3.85 mm
