nexxyz/octessera/hardware/enclosure/3mf-multicolor/standoff_pillar_9_5mm.3mf

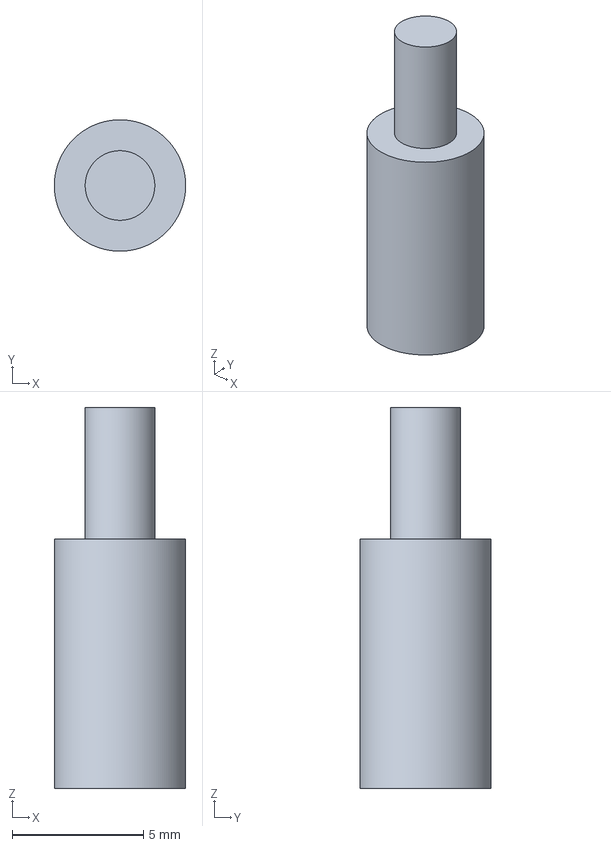
[picture p25: CAD file, 2026-09-15]
hardware/enclosure/3mf-multicolor/standoff_pillar_9_5mm.3mf
5.00 x 5.00 x 14.5 mm
