nexxyz/octessera/hardware/enclosure/3mf-single-material/mx_keycap_play.3mf

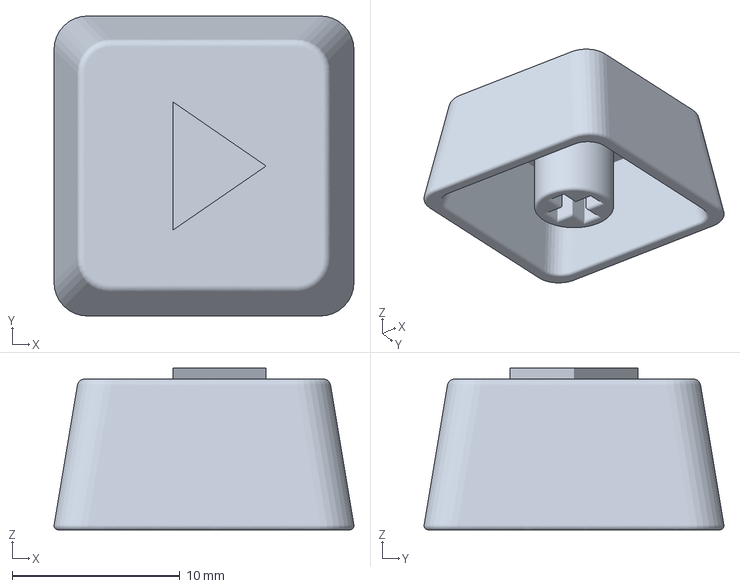
[picture p26: CAD file, 2026-09-15]
hardware/enclosure/3mf-single-material/mx_keycap_play.3mf
17.9 x 17.9 x 9.65 mm
