nexxyz/octessera/userdocs/hardware/images/assembly/pi-zero-2w.jpg

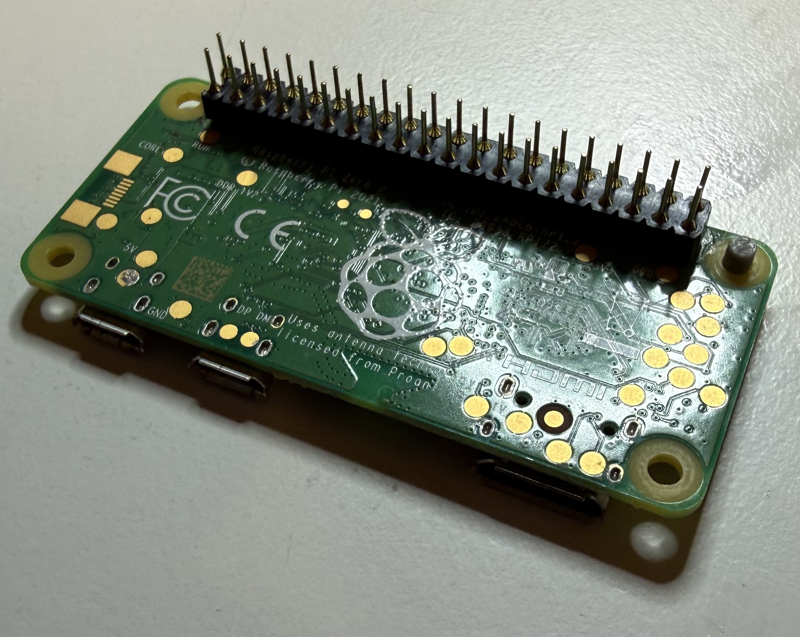
userdocs/hardware/images/assembly/pi-zero-2w.jpg
