nexxyz/octessera/apps/pi-zero/src/main_paths.rs

#[cfg(not(feature = "hardware-orange-pi-zero-2w"))]
use std::path::Path;
use std::path::PathBuf;

const STORE_DIR_ENV: &str = "OCTESSERA_PI_STORE_DIR";
const SAMPLES_DIR_ENV: &str = "OCTESSERA_PI_SAMPLES_DIR";
const RECORDINGS_DIR_ENV: &str = "OCTESSERA_PI_RECORDINGS_DIR";
const SCREEN_RECORDINGS_DIR_ENV: &str = "OCTESSERA_PI_SCREEN_RECORDINGS_DIR";
const RASPBERRY_RECORDINGS_DIR: &str = "/home/pi/recordings";
const RASPBERRY_SCREEN_RECORDINGS_DIR: &str = "/home/pi/screen-recordings";
const ORANGE_RECORDINGS_DIR: &str = "/var/lib/octessera/recordings";
const ORANGE_SCREEN_RECORDINGS_DIR: &str = "/var/lib/octessera/screen-recordings";

pub(crate) fn default_store_dir() -> PathBuf {
    configured_dir(STORE_DIR_ENV, "presets")
}

#[cfg(not(feature = "hardware-orange-pi-zero-2w"))]
pub(crate) fn ensure_runtime_dirs(store_dir: &Path, samples_dir: &Path) {
    let _ = std::fs::create_dir_all(samples_dir);
    let _ = std::fs::create_dir_all(store_dir);
}

#[cfg(not(feature = "hardware-orange-pi-zero-2w"))]
pub(crate) fn ensure_samples_dir(samples_dir: &Path) -> Result<(), String> {
    std::fs::create_dir_all(samples_dir)
        .map_err(|error| format!("Pi samples directory is not usable: {error}"))?;
    let metadata = std::fs::metadata(samples_dir)
        .map_err(|error| format!("Pi samples directory cannot be inspected: {error}"))?;
    if !metadata.is_dir() {
        return Err(format!(
            "Pi samples path is not a directory: {}",
            samples_dir.display()
        ));
    }
    Ok(())
}

pub(crate) fn default_samples_dir() -> PathBuf {
    configured_dir(SAMPLES_DIR_ENV, "samples")
}

pub(crate) fn default_recordings_dir() -> PathBuf {
    configured_media_dir(
        RECORDINGS_DIR_ENV,
        RASPBERRY_RECORDINGS_DIR,
        ORANGE_RECORDINGS_DIR,
    )
}

pub(crate) fn default_screen_recordings_dir() -> PathBuf {
    configured_media_dir(
        SCREEN_RECORDINGS_DIR_ENV,
        RASPBERRY_SCREEN_RECORDINGS_DIR,
        ORANGE_SCREEN_RECORDINGS_DIR,
    )
}

#[cfg(feature = "hardware-orange-pi-zero-2w")]
fn configured_media_dir(_environment_variable: &str, _raspberry: &str, orange: &str) -> PathBuf {
    PathBuf::from(orange)
}

#[cfg(not(feature = "hardware-orange-pi-zero-2w"))]
fn configured_media_dir(environment_variable: &str, raspberry: &str, _orange: &str) -> PathBuf {
    configured_media_dir_from(
        std::env::var_os(environment_variable).map(PathBuf::from),
        raspberry,
    )
}

#[cfg(not(feature = "hardware-orange-pi-zero-2w"))]
fn configured_media_dir_from(configured: Option<PathBuf>, raspberry: &str) -> PathBuf {
    configured.unwrap_or_else(|| PathBuf::from(raspberry))
}

fn configured_dir(environment_variable: &str, fallback_name: &str) -> PathBuf {
    configured_dir_from(
        std::env::var_os(environment_variable).map(PathBuf::from),
        home_dir(),
        fallback_name,
    )
}

fn configured_dir_from(
    configured: Option<PathBuf>,
    home: Option<PathBuf>,
    fallback_name: &str,
) -> PathBuf {
    configured.unwrap_or_else(|| {
        home.map(|home| home.join(fallback_name))
            .unwrap_or_else(|| PathBuf::from(fallback_name))
    })
}

fn home_dir() -> Option<PathBuf> {
    std::env::var_os("HOME").map(PathBuf::from)
}

#[cfg(test)]
mod tests {
    #[cfg(not(feature = "hardware-orange-pi-zero-2w"))]
    use super::configured_media_dir_from;
    #[cfg(not(feature = "hardware-orange-pi-zero-2w"))]
    use super::ensure_samples_dir;
    use super::{configured_dir_from, SAMPLES_DIR_ENV, STORE_DIR_ENV};
    #[cfg(feature = "hardware-orange-pi-zero-2w")]
    use super::{default_recordings_dir, default_screen_recordings_dir};
    use std::path::PathBuf;

    #[test]
    fn orange_path_contract_uses_explicit_pi_environment_variables() {
        assert_eq!(STORE_DIR_ENV, "OCTESSERA_PI_STORE_DIR");
        assert_eq!(SAMPLES_DIR_ENV, "OCTESSERA_PI_SAMPLES_DIR");
        assert_eq!(
            configured_dir_from(
                Some(PathBuf::from("configured/presets")),
                Some(PathBuf::from("home")),
                "presets",
            ),
            PathBuf::from("configured/presets")
        );
        assert_eq!(
            configured_dir_from(
                Some(PathBuf::from("configured/samples")),
                Some(PathBuf::from("home")),
                "samples",
            ),
            PathBuf::from("configured/samples")
        );
    }

    #[test]
    fn path_contract_falls_back_to_home_only_when_unconfigured() {
        assert_eq!(
            configured_dir_from(None, Some(PathBuf::from("home")), "presets"),
            PathBuf::from("home/presets")
        );
        assert_eq!(
            configured_dir_from(None, None, "samples"),
            PathBuf::from("samples")
        );
    }

    #[cfg(not(feature = "hardware-orange-pi-zero-2w"))]
    #[test]
    fn raspberry_media_roots_preserve_the_existing_absolute_paths() {
        assert_eq!(
            configured_media_dir_from(None, "/home/pi/recordings"),
            PathBuf::from("/home/pi/recordings")
        );
        assert_eq!(
            configured_media_dir_from(None, "/home/pi/screen-recordings"),
            PathBuf::from("/home/pi/screen-recordings")
        );
        assert_eq!(
            configured_media_dir_from(Some(PathBuf::from("configured/recordings")), "unused"),
            PathBuf::from("configured/recordings")
        );
    }

    #[cfg(feature = "hardware-orange-pi-zero-2w")]
    #[test]
    fn orange_media_roots_are_explicitly_outside_protected_home() {
        assert_eq!(
            default_recordings_dir(),
            PathBuf::from("/var/lib/octessera/recordings")
        );
        assert_eq!(
            default_screen_recordings_dir(),
            PathBuf::from("/var/lib/octessera/screen-recordings")
        );
    }

    #[cfg(not(feature = "hardware-orange-pi-zero-2w"))]
    #[test]
    fn sample_root_creation_failure_is_returned() {
        let root = crate::test_temp_dir::unique_temp_path("octessera-pi-samples-root");
        std::fs::create_dir_all(&root).unwrap();
        let path = root.join("samples");
        std::fs::write(&path, b"not a directory").unwrap();
        let marker = root.join("candidate-ready.json");
        let readiness = crate::candidate_readiness::CandidateReadiness::new(
            Some(marker.clone()),
            "pi-sample-root-failure".into(),
        );

        let error = ensure_samples_dir(&path).unwrap_err();

        assert!(error.contains("Pi samples directory is not usable"));
        assert!(!marker.exists());
        drop(readiness);
        let _ = std::fs::remove_dir_all(root);
    }
}
