nexxyz/octessera/apps/pi-zero/src/render.rs

#![cfg_attr(feature = "hardware-orange-pi-zero-2w", allow(dead_code))]

use crate::oled_frame_cache::{OledFrameKey, OledFramePublication};
use crate::seesaw_io::SeesawCommand;
use octessera_hal::OledSsd1351;
use serde_json::Value;
use std::sync::mpsc::Sender;
use std::time::Instant;

pub(crate) mod hdmi;
mod native_leds;
mod native_publication;
pub(crate) use native_publication::{
    prepare_legacy_presentation, prepare_native_scene, LatestPresentation,
};
mod oled;
mod oled_output;
mod oled_ownership;
mod ownership_control;
mod ownership_decision;
mod sleep_leds;

#[cfg(all(test, not(feature = "hardware-orange-pi-zero-2w")))]
pub(crate) mod test_oled_output;

#[cfg(all(test, not(feature = "hardware-orange-pi-zero-2w")))]
pub(crate) type OledRenderOutput = test_oled_output::TestOledOutput;
#[cfg(not(all(test, not(feature = "hardware-orange-pi-zero-2w"))))]
pub(crate) type OledRenderOutput = OledSsd1351;

pub(crate) use oled::OLED_FRAME_BYTES;
#[cfg(test)]
use oled::{glyph_rows, oled_frame, oled_frame_into};
pub(crate) use oled_output::physical_oled_publication;
pub(crate) use oled_output::retry_oled_if_due;
#[cfg(all(test, not(feature = "hardware-orange-pi-zero-2w")))]
use oled_output::OledRenderDevice;
use oled_output::{force_oled_render, render_oled_if_changed};
pub(crate) use oled_ownership::{
    handle_stage, restore, restore_after_dropped_ack, OledOwnershipStage, OledOwnershipState,
    OledRenderControl,
};
pub(crate) use ownership_control::{
    ownership_stage_for_render, restore_after_dropped_ack_for_render, restore_for_render,
};
pub(crate) use ownership_decision::{
    initial_snapshot_render_result, mark_handoff_failed_decision, retry_oled_decision,
    select_snapshot_render, snapshot_requires_oled_ack, SnapshotRenderDecision,
};
use sleep_leds::{SleepLedAnimation, SleepLedFrames};

#[derive(Clone, Copy, Debug, Eq, PartialEq)]
pub(super) struct OledOutputKey {
    pub(super) frame: OledFrameKey,
    pub(super) display_off: bool,
}

impl OledOutputKey {
    pub(super) fn new(frame: OledFrameKey, display_off: bool) -> Self {
        Self { frame, display_off }
    }
}

#[derive(Default)]
pub(super) struct OledOutputState {
    pub(super) frame: Option<OledFrameKey>,
    pub(super) display_off: Option<bool>,
    pub(super) pixels: Option<Vec<u8>>,
    pub(super) physical_revision: u64,
}

const SPLASH_BOOT: &[u8] = include_bytes!(concat!(env!("OUT_DIR"), "/splash_boot.rgb565"));
const SPLASH_SLEEP_SHUTDOWN: &[u8] =
    include_bytes!(concat!(env!("OUT_DIR"), "/splash_sleep_shutdown.rgb565"));
const SLEEP_DIM_SCALE: f32 = 0.08;
const MIN_SLEEP_DIM_SCALE: f32 = 0.04;

pub(crate) fn shutdown_splash_base_frame() -> Vec<u8> {
    SPLASH_SLEEP_SHUTDOWN.to_vec()
}

mod boot_sweep;
#[cfg(all(test, not(feature = "hardware-orange-pi-zero-2w")))]
pub(crate) use boot_sweep::{
    boot_sweep_base_frame, boot_sweep_bottom_row_origin, boot_sweep_deadline_offset_ns,
    boot_sweep_frame, boot_sweep_frame_from, boot_sweep_frames, logical_to_physical_bottom,
    physical_to_logical_input, rgb565_at, BOOT_SWEEP_BAND_WIDTH, BOOT_SWEEP_COLORS,
    BOOT_SWEEP_CYCLE_NS, BOOT_SWEEP_FRAMES, BOOT_SWEEP_LEAN_DENOMINATOR, BOOT_SWEEP_LEAN_NUMERATOR,
    BOOT_SWEEP_REST_CHECK_NS, BOOT_SWEEP_REST_NS, BOOT_SWEEP_SEPARATOR_COLOR,
    BOOT_SWEEP_SEPARATOR_WIDTH, BOOT_SWEEP_TRAIN_WIDTH,
};
#[cfg(all(not(test), not(feature = "hardware-orange-pi-zero-2w")))]
pub(crate) use boot_sweep::{
    boot_sweep_base_frame, boot_sweep_frames, BOOT_SWEEP_CYCLE_NS, BOOT_SWEEP_FRAMES,
    BOOT_SWEEP_REST_CHECK_NS, BOOT_SWEEP_REST_NS,
};
#[cfg(not(feature = "hardware-orange-pi-zero-2w"))]
pub(crate) use boot_sweep::{boot_sweep_deadline, render_boot_splash};
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
